Eyjafjallajokull/atmega-pinhole/design/pcb-design-generated/pcb-design_etch_silk_bottom.pdf

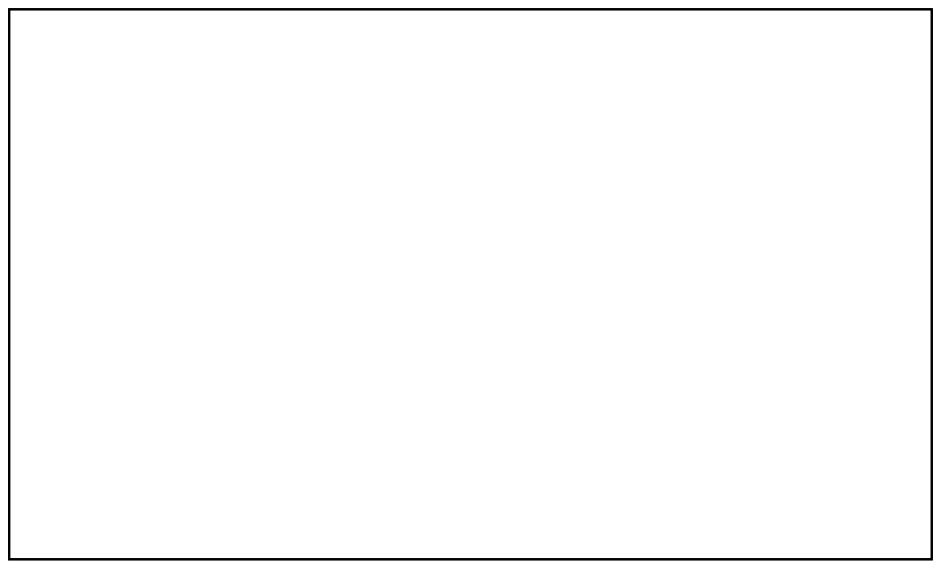
[picture p13: page 1]
