Eyjafjallajokull/atmega-pinhole/design/pcb-design-generated/pcb-design_etch_silk_bottom_mirror.pdf

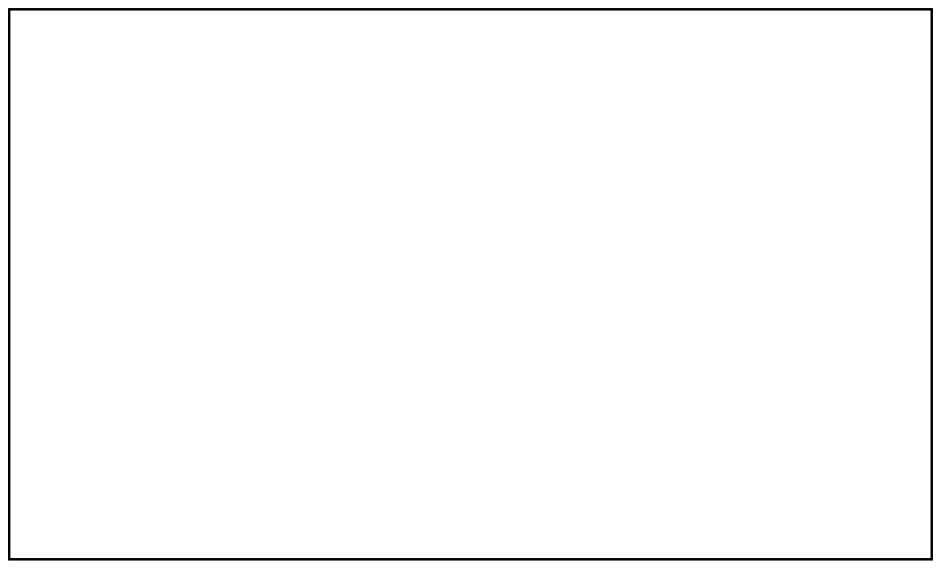
[picture p14: page 1]
