Eyjafjallajokull/atmega-pinhole/design/pcb-design-generated/pcb-design_etch_silk_top.pdf

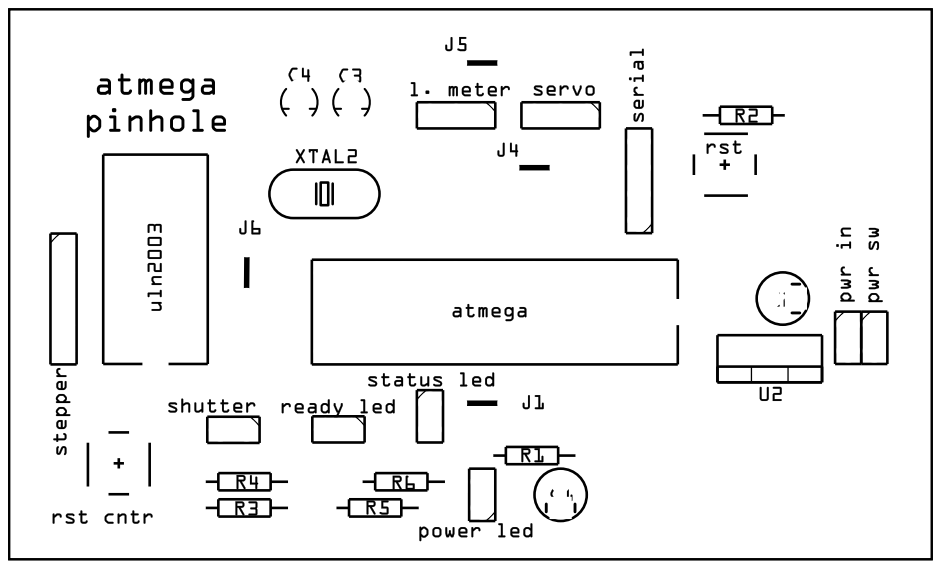
[picture p15: page 1]
