Eyjafjallajokull/atmega-pinhole/design/pcb-design-generated/pcb-design_etch_silk_top_mirror.pdf

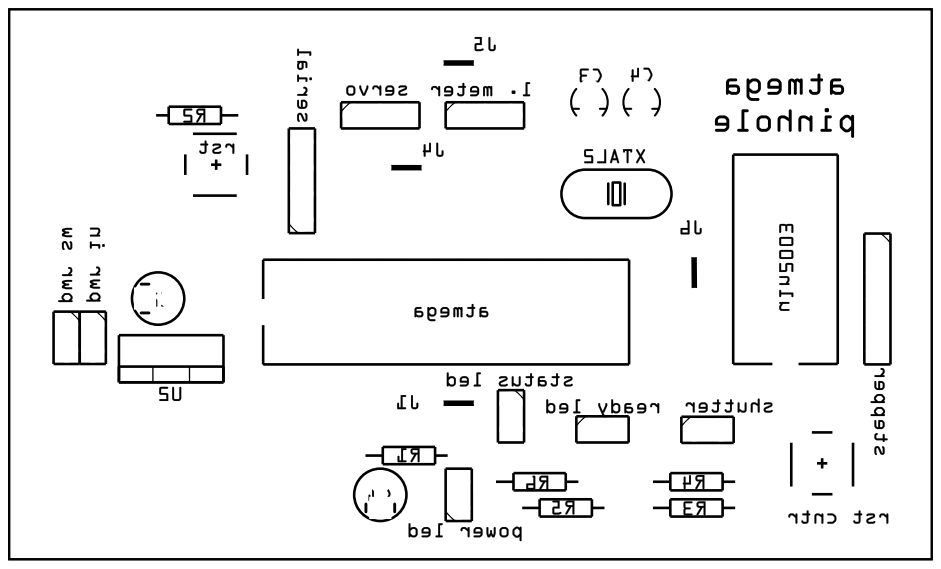
[picture p16: page 1]
